disq/ledcontrol/enclosure/IMG_1634.jpg

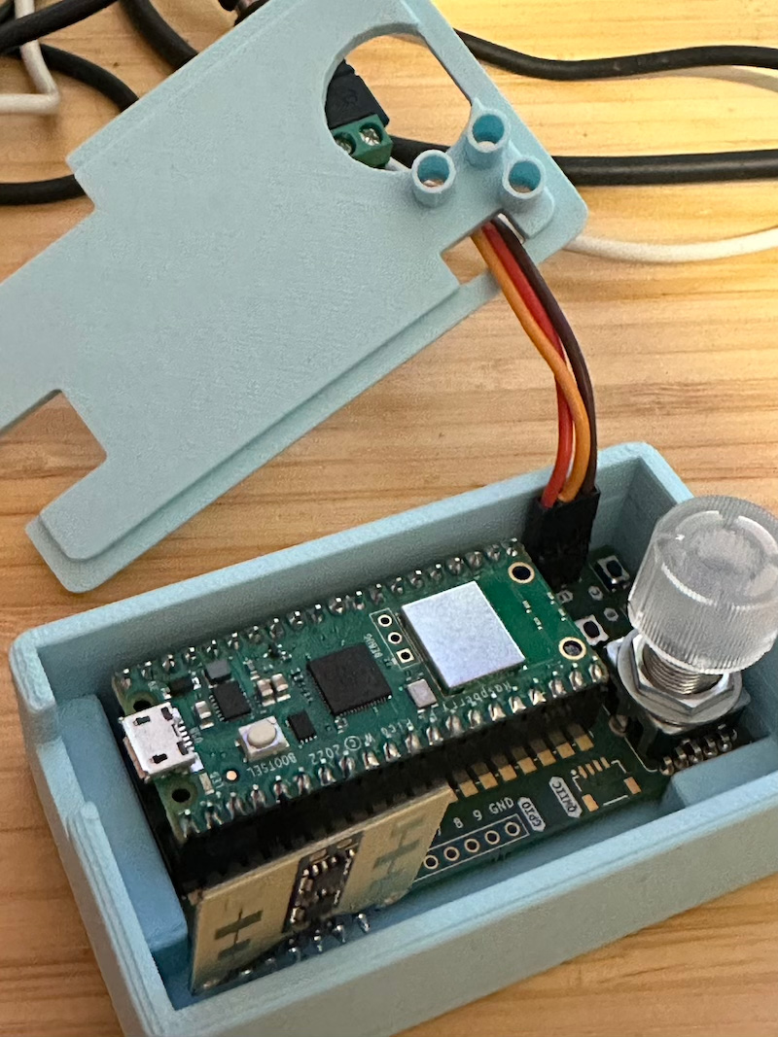
enclosure/IMG_1634.jpg
