disq/ledcontrol/enclosure/IMG_1635.jpg

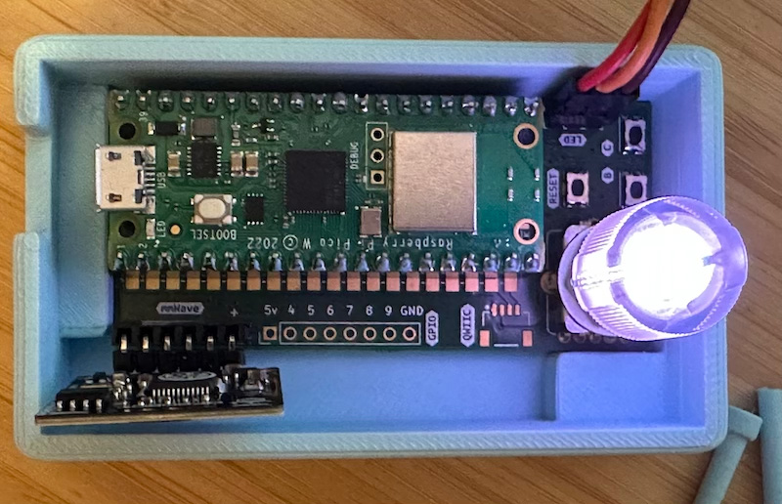
enclosure/IMG_1635.jpg
