disq/ledcontrol/enclosure/IMG_1636.jpg

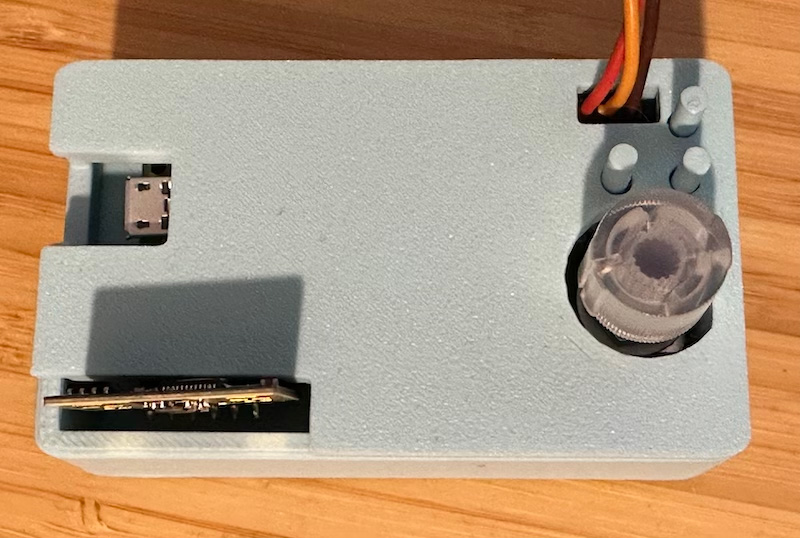
enclosure/IMG_1636.jpg
