disq/ledcontrol/pcb1/IMG_1640.jpg

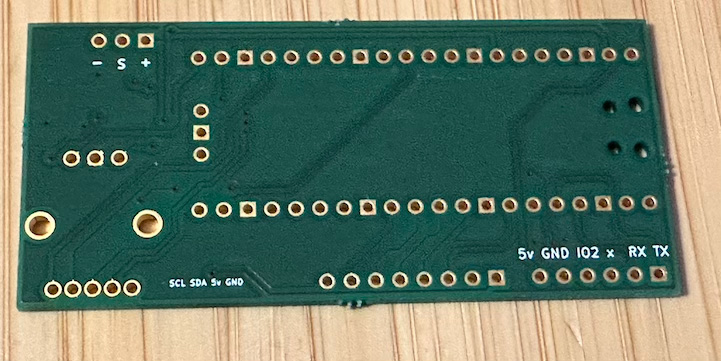
pcb1/IMG_1640.jpg
