disq/ledcontrol/pcb2/IMG_1870.jpg

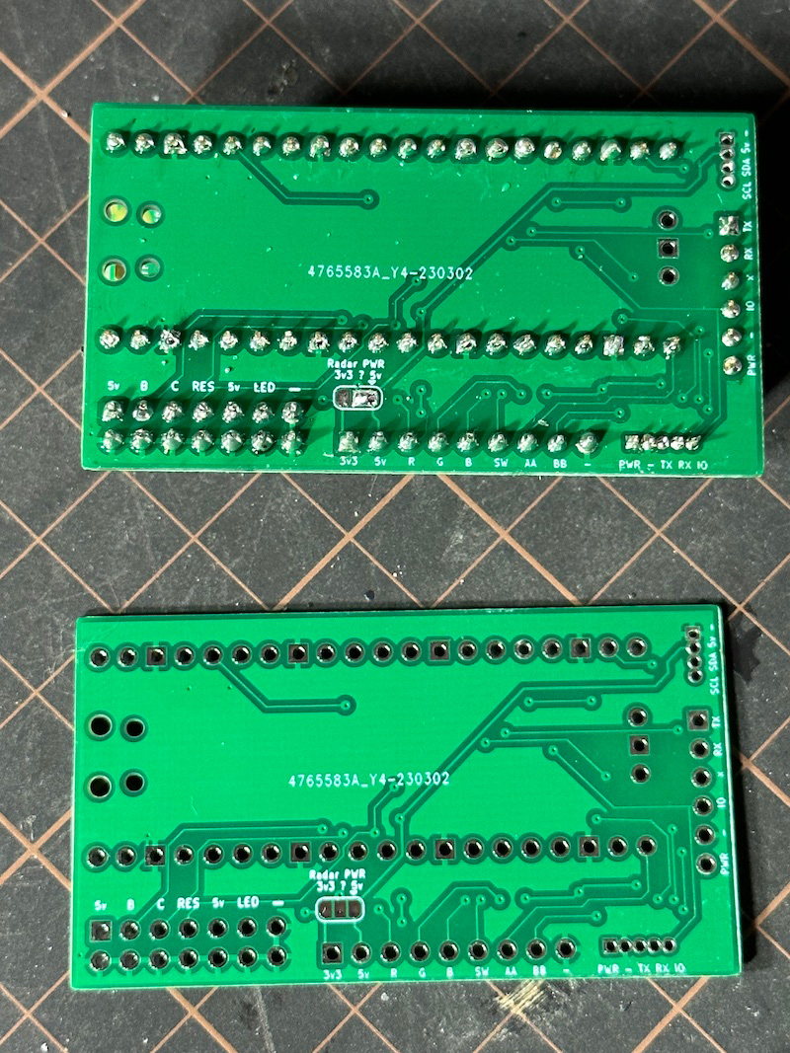
pcb2/IMG_1870.jpg
